SQ5BAR/piHPSDR-MIDI-Console/tusb_config.h

#pragma once
#define CFG_TUSB_MCU              OPT_MCU_RP2040
#define CFG_TUSB_RHPORT0_MODE     (OPT_MODE_DEVICE)
#define CFG_TUSB_OS              OPT_OS_PICO
#define CFG_TUD_ENDPOINT0_SIZE    64
#define CFG_TUD_MIDI              1
#define CFG_TUD_MIDI_RX_BUFSIZE   64
#define CFG_TUD_MIDI_TX_BUFSIZE   64

#define CFG_TUD_CDC              1
#define CFG_TUD_CDC_RX_BUFSIZE    256
#define CFG_TUD_CDC_TX_BUFSIZE    256
